tkm3d1a/TKKB-design-r1/Pictures/GMK Stealth Order - Base Kit.png

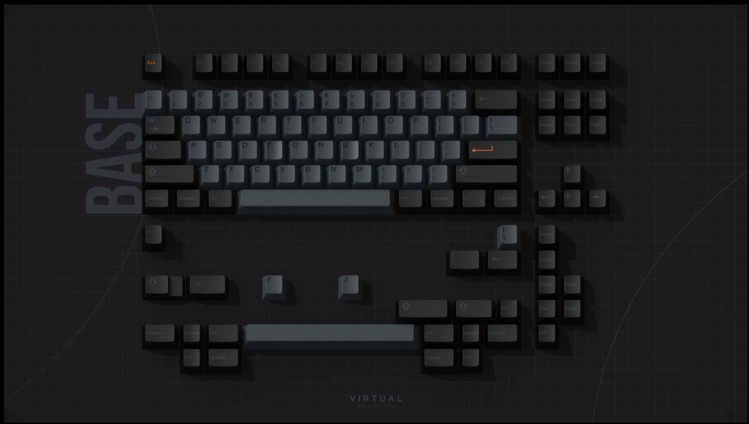
Pictures/GMK Stealth Order - Base Kit.png
