tkm3d1a/TKKB-design-r1/CAD Files/9262K511_MULTIPURPOSE O-RING.SLDPRT

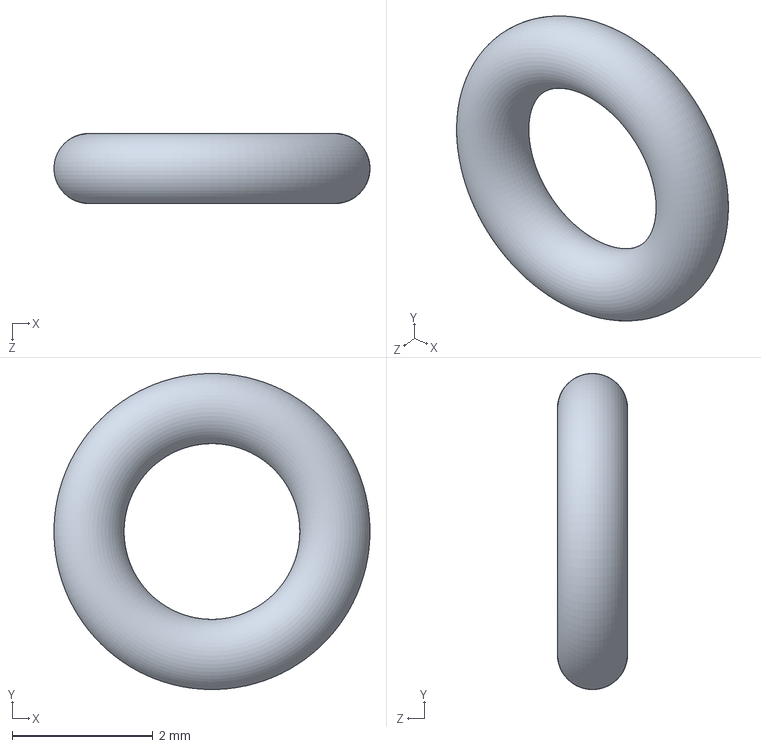
[picture p22: CAD file, 2021-01-16]
CAD Files/9262K511_MULTIPURPOSE O-RING.SLDPRT
4.50 x 4.50 x 1 mm
